BrianHan113/IoT-HomeAutomation-ESP32/nextion-HMI/images/tides.png

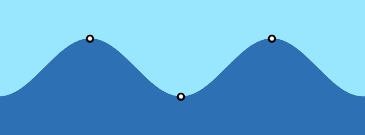
nextion-HMI/images/tides.png
