BrianHan113/IoT-HomeAutomation-ESP32/esp32-LED-strip/src/main.cpp

// Copyright (c) 2025 RisosEnterprises Ltd. All rights reserved.
// Developed by RisosEnterprises Ltd, Auckland, New Zealand.
// Licensed under Creative Commons Attribution-NonCommercial 4.0 International (CC BY-NC 4.0).
// See https://creativecommons.org/licenses/by-nc/4.0/ for details.
// Author: Brian Han

#include <Arduino.h>
#include <FastLED.h>
#include <receiver_espnow.h>

#define HW_NUM_LEDS 19 // Number of LEDs in the strip, change this to your strip length
#define DATA_PIN 26

String EspID = "LED_STRIP";
CRGB leds[HW_NUM_LEDS];

uint8_t red = 255;
uint8_t green = 255;
uint8_t blue = 255;

CRGB colour;

int NUM_LEDS = -1;
bool isStripOn = false;

void setup()
{
  Serial.begin(115200);
  WiFi.mode(WIFI_STA);
  WiFi.disconnect();
  esp_wifi_set_channel(1, WIFI_SECOND_CHAN_NONE);

  esp_now_init();

  esp_now_register_send_cb(OnDataSent);
  esp_now_register_recv_cb(OnDataRecv);
  // FastLED supports many other LED Strips, enter your own here
  FastLED.addLeds<WS2815, DATA_PIN, RGB>(leds, HW_NUM_LEDS);
  FastLED.clear();
}

void loop()
{

  if (NUM_LEDS > 0) // check NUM_LEDS is configured in nextion settings
  {
    if (isStripOn)
    {
      colour = CRGB(red, green, blue);
      FastLED.clear();
      for (int i = 0; i < min(NUM_LEDS, HW_NUM_LEDS); i++)
      {
        leds[i] = colour;
      }
    }
    else
    {
      FastLED.clear();
    }
    FastLED.show();
  }

  vTaskDelay(100 / portTICK_PERIOD_MS);
}
