BrianHan113/IoT-HomeAutomation-ESP32/esp32-HW-monitor/src/utils.cpp

// Copyright (c) 2025 RisosEnterprises Ltd. All rights reserved.
// Developed by RisosEnterprises Ltd, Auckland, New Zealand.
// Licensed under Creative Commons Attribution-NonCommercial 4.0 International (CC BY-NC 4.0).
// See https://creativecommons.org/licenses/by-nc/4.0/ for details.
// Author: Brian Han

#include "utils.h"

extern HardwareSerial nextion;
extern QueueHandle_t sendNextionQueue;

void queueNextionCommand(String command)
{
    if (xQueueSend(sendNextionQueue, command.c_str(), 0) != pdTRUE)
    {
        Serial.println("Queue Full, Send Nextion Command Dropped!");
    }
}

void sendNextionCommand(String command)
{
    nextion.print(command);
    nextion.write(0xFF);
    nextion.write(0xFF);
    nextion.write(0xFF);
}

uint32_t nextionNumConvert(int start, int end, String command)
{
    int len = end - start;
    uint8_t numberData[len];
    uint32_t commandNumData = 0;

    // Nextion sends number data in little-endian format, so reverse it
    for (int i = 0; i < len; i++)
    {
        numberData[len - 1 - i] = static_cast<uint8_t>(command.charAt(start + i));
    }

    // Merge bytes
    for (int i = 0; i < len; i++)
    {
        commandNumData = (commandNumData << 8) | numberData[i]; // Shift and add the next byte
    }

    return commandNumData;
}

void nextionWaveformYAxisScale(int min, int max, String waveformID)
{
    int currVal = min;
    int step = (max - min) / 5;
    for (int i = 0; i <= 5; i++)
    {
        queueNextionCommand(waveformID + i + ".txt=\"" + currVal + "\"");
        currVal += step;
    }
}

float calculateAverage(const float arr[], int size)
{
    float sum = 0.0;
    int count = 0;

    for (int i = 0; i < size; i++)
    {
        if (arr[i] != 0.0)
        {
            sum += arr[i];
            count++;
        }
    }

    return count > 0 ? sum / count : 0.0;
}

void sendCommandToDevice(String command, String device)
{
    std::array<uint8_t, 6> MAC = deviceMACMap[device];

    char dataToSend[32];
    strncpy(dataToSend, command.c_str(), sizeof(dataToSend) - 1);
    dataToSend[sizeof(dataToSend) - 1] = '\0';

    esp_err_t result = esp_now_send(MAC.data(), (uint8_t *)&dataToSend, sizeof(dataToSend));

    if (result == ESP_OK)
    {
        Serial.println("Sending " + String(dataToSend) + " confirmed to " + device + " with MAC: ");
    }
    else
    {
        Serial.println("Sending " + String(dataToSend) + " error to " + device + " with MAC: ");
    }
    displayMacAddress(MAC);
}

// WEATHER STUFF - a lot of hard coding ids, but it's unavoidable due to how images are stored on the Nextion display
int weatherCodeToNextionPicID(int code, bool isDay)
{
    if (code == 0) // Clear
    {
        return isDay ? 0 : 1;
    }
    else if (code == 1) // Partly cloudy
    {
        return isDay ? 2 : 3;
    }
    else if (code == 2) // Cloudy
    {
        return 4;
    }
    else if (code == 3) // Overcast
    {
        return 6;
    }
    else if (code == 45 || code == 48) // Fog
    {
        return 16;
    }
    else if (code >= 51 && code <= 57) // Drizzle
    {
        return isDay ? 2 : 3;
    }
    else if (code >= 61 && code <= 67) // Rain
    {
        return 6;
    }
    else if (code >= 80 && code <= 82) // Shower
    {
        return 6;
    }
    else if ((code >= 71 && code <= 77) || (code == 85 || code == 86)) // Snow
    {
        return 14;
    }
    else if (code >= 95 && code <= 99) // Thunderstorm
    {
        return 12;
    }
    else
    {
        return 19; // Unknown
    }
}

int windSpeedToNextionPicID(float windSpeed)
{
    int windKnotsRounded = (round(windSpeed * 0.539957 / 5) * 5);

    // Follows Beufort wind scale
    if (windKnotsRounded == 0) // No wind
    {
        return 19;
    }
    else if (windKnotsRounded == 5 || windKnotsRounded == 10) // low wind
    {
        return 21;
    }
    else if (windKnotsRounded == 15 || windKnotsRounded == 20) // moderate wind
    {
        return 22;
    }
    else if (windKnotsRounded > 20) // strong wind
    {
        return 20;
    }
    else
    {
        return 19;
    }
}

int rainToNextionRainID(float prec, int prec_probability)
{
    String imgName = "";

    if (prec < 0.5) // No rain
    {
        return 19;
    }
    else if (prec >= 0.5 && prec <= 1.0) // 1 raindrop
    {
        imgName += "1";
    }
    else if (prec > 1.0 && prec <= 2.0) // 2 raindrops
    {
        imgName += "2";
    }
    else if (prec > 2.0 && prec <= 4.0) // 3 raindrops
    {
        imgName += "3";
    }
    else if (prec > 4.0) // 4 raindrops
    {
        imgName += "4";
    }

    if (prec_probability < 30) // Light blue
    {
        imgName += "low";
    }
    else if (prec_probability >= 30 && prec_probability <= 60) // Blue
    {
        imgName += "mid";
    }
    else if (prec_probability > 60) // Dark blue
    {
        imgName += "high";
    }

    if (imgName == "1high")
    {
        return 91;
    }
    else if (imgName == "1low")
    {
        return 92;
    }
    else if (imgName == "1mid")
    {
        return 93;
    }
    else if (imgName == "2high")
    {
        return 94;
    }
    else if (imgName == "2low")
    {
        return 95;
    }
    else if (imgName == "2mid")
    {
        return 96;
    }
    else if (imgName == "3high")
    {
        return 97;
    }
    else if (imgName == "3low")
    {
        return 98;
    }
    else if (imgName == "3mid")
    {
        return 99;
    }
    else if (imgName == "4high")
    {
        return 100;
    }
    else if (imgName == "4low")
    {
        return 101;
    }
    else if (imgName == "4mid")
    {
        return 102;
    }
    return 19; // Unknown
}

int windToNextionWindBarbID(float windSpeed, int windDir)
{

    int windKnots = (round(windSpeed * 0.539957 / 5) * 5);

    if (windKnots == 0) // Calm
    {
        return 25;
    }

    String cardinalDir;

    if (windDir >= 0 && windDir <= 22 || windDir > 337 && windDir <= 360)
    {
        cardinalDir = "S"; // Assuming cardinal direction is opposite of wind, i.e. wind coming from the north means wind is blowing south
    }
    else if (windDir > 22 && windDir <= 67)
    {
        cardinalDir = "SW";
    }
    else if (windDir > 67 && windDir <= 112)
    {
        cardinalDir = "W";
    }
    else if (windDir > 112 && windDir <= 157)
    {
        cardinalDir = "NW";
    }
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
        }
        else if (windKnots == 30)
        {
            return 55;
        }
        else if (windKnots == 35)
        {
            return 56;
        }
        else if (windKnots == 40)
        {
            return 57;
        }
    }

    return 19; // Unknown
}
